proboterror/smd2wii/wiimote.h

#pragma once

#include "defines.h"
#include <string.h>
#include <avr/io.h>
#include <util/delay.h>
#include <util/twi.h>
#include <avr/interrupt.h>

extern volatile unsigned char twi_reg[256];
extern volatile unsigned int twi_reg_addr;

// initialize wiimote interface with id, starting data, and calibration data
void wm_init(unsigned char *, unsigned char *, void (*)(void));

// set button data
void wm_newaction(unsigned char *);
